Silcris26/Rover-Gale/Diagramas/Diagrama Caja Negra.png

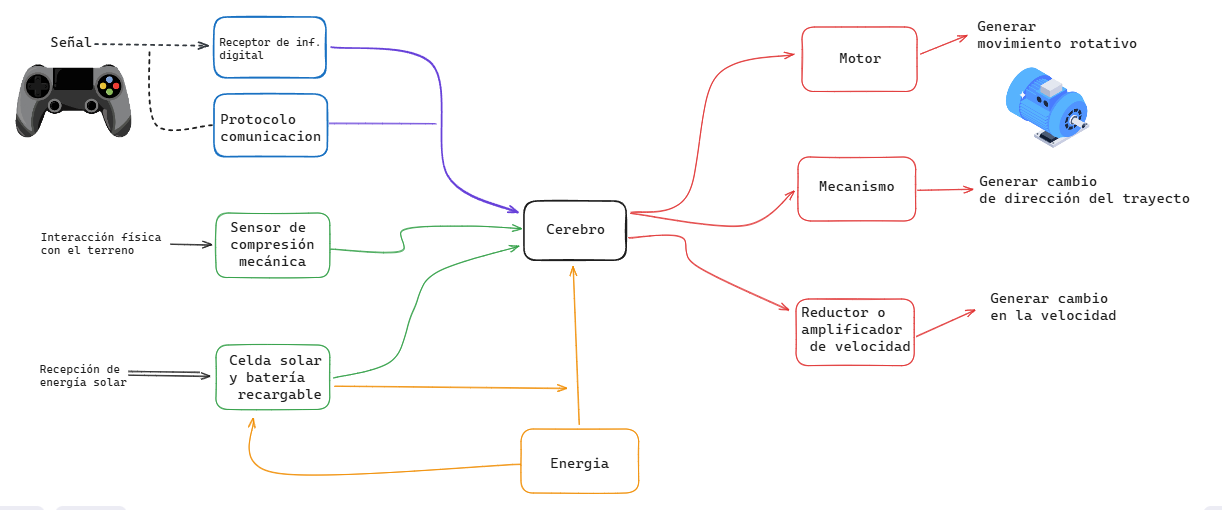
Diagramas/Diagrama Caja Negra.png
