Silcris26/Rover-Gale/Diagramas/Diagrama Codigo.png

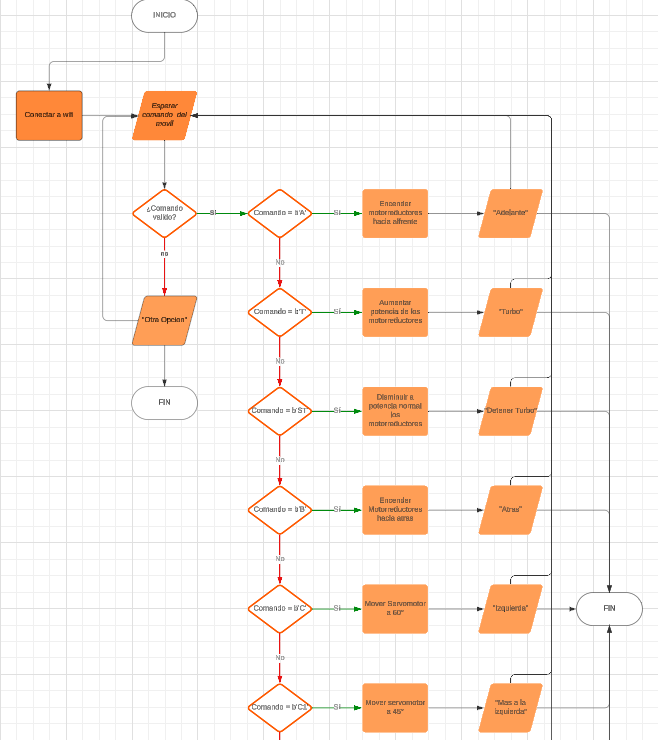
Diagramas/Diagrama Codigo.png
