Silcris26/Rover-Gale/Diagramas/Diagrama tecnologia.PNG

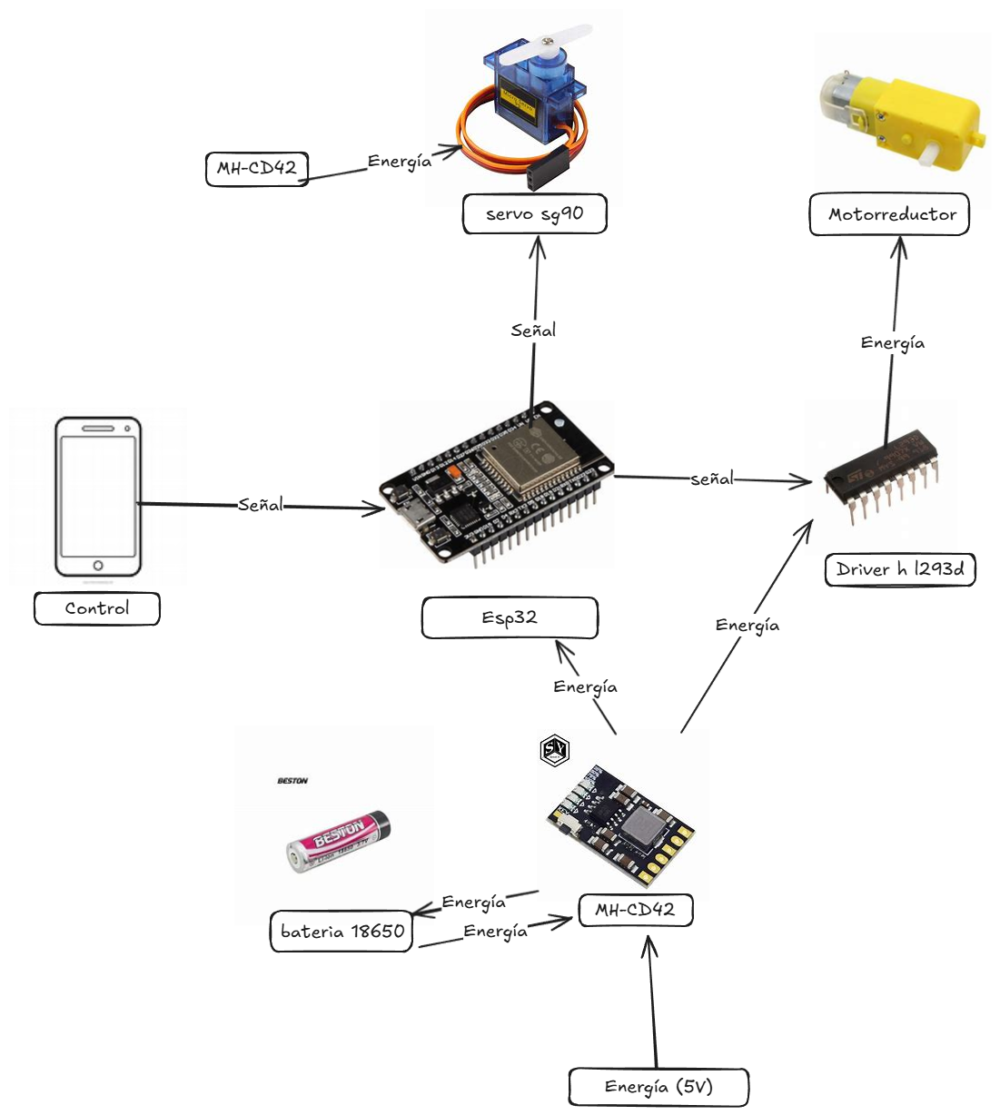
Diagramas/Diagrama tecnologia.PNG
