Silcris26/Rover-Gale/Diseño 3D/1.jpg

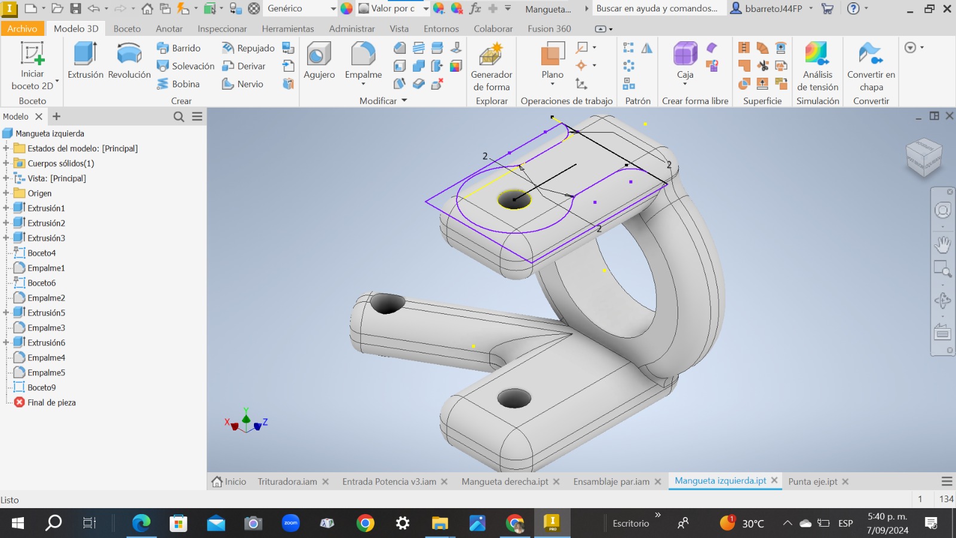
Diseño 3D/1.jpg
