Silcris26/Rover-Gale/Diseño 3D/2.jpg

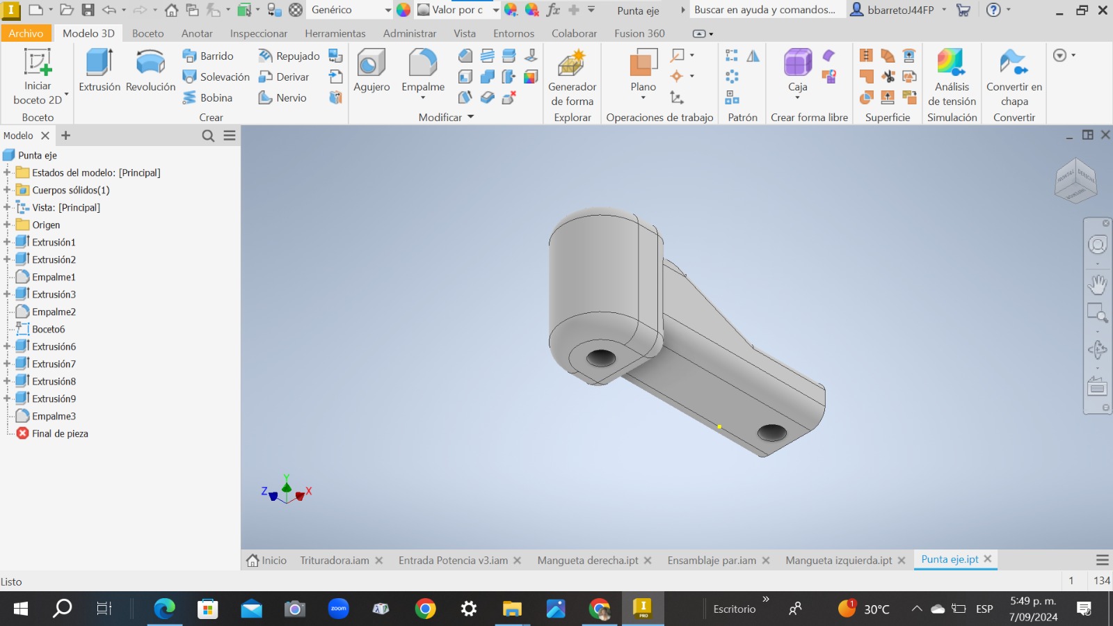
Diseño 3D/2.jpg
