Silcris26/Rover-Gale/Diseño 3D/4.jpg

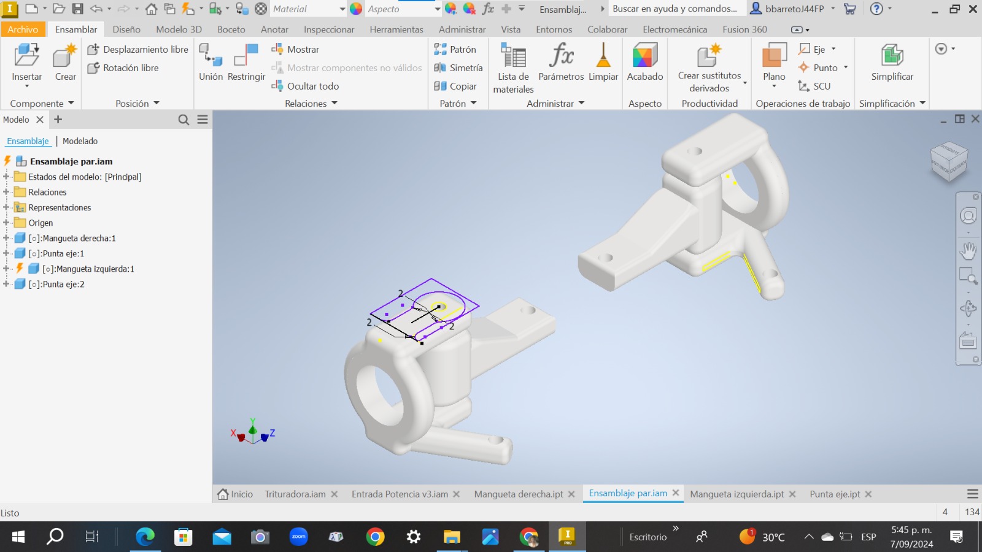
Diseño 3D/4.jpg
