Silcris26/Rover-Gale/Diseño 3D/5.jpg

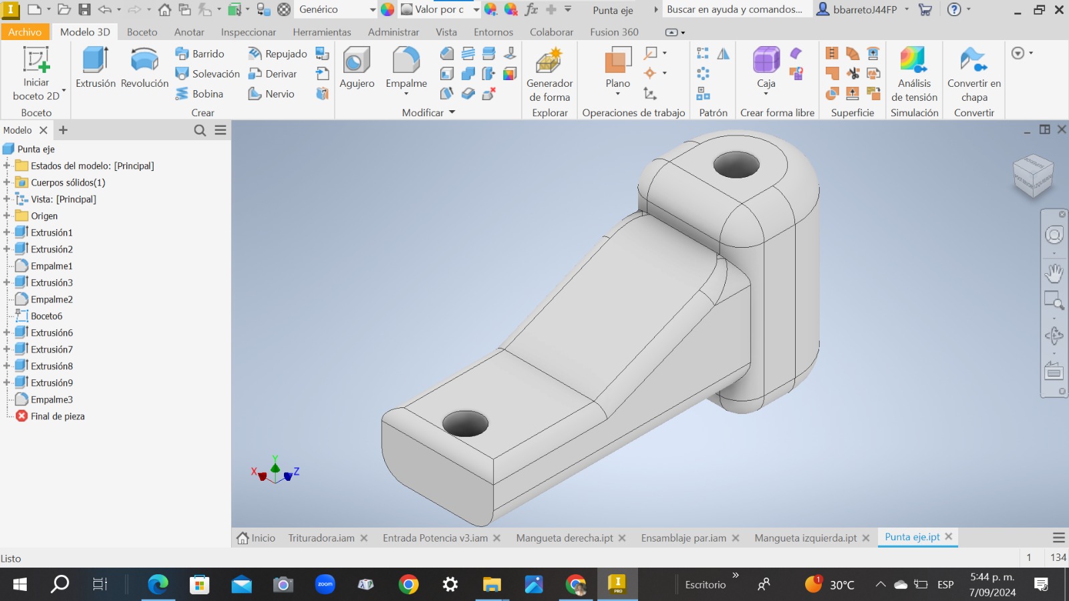
Diseño 3D/5.jpg
