Silcris26/Rover-Gale/Diseño 3D/7.jpg

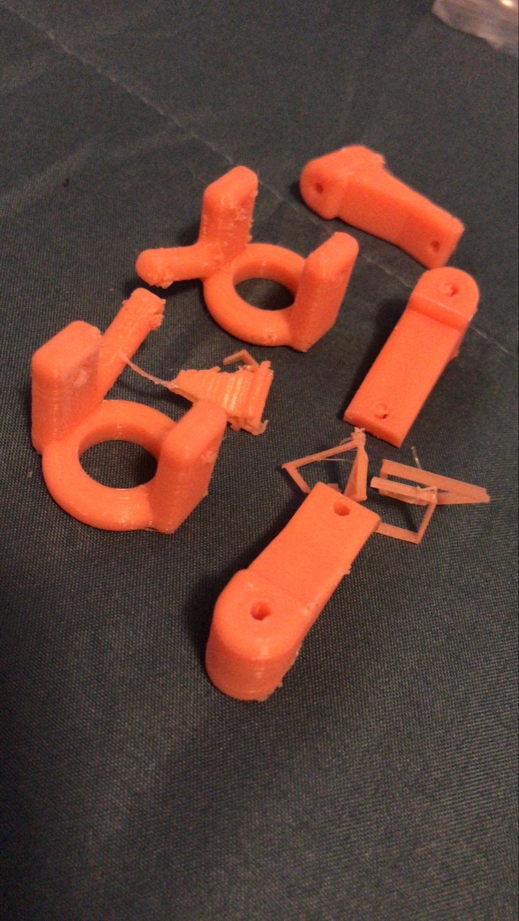
Diseño 3D/7.jpg
