Silcris26/Rover-Gale/Diseño 3D/8.jpg

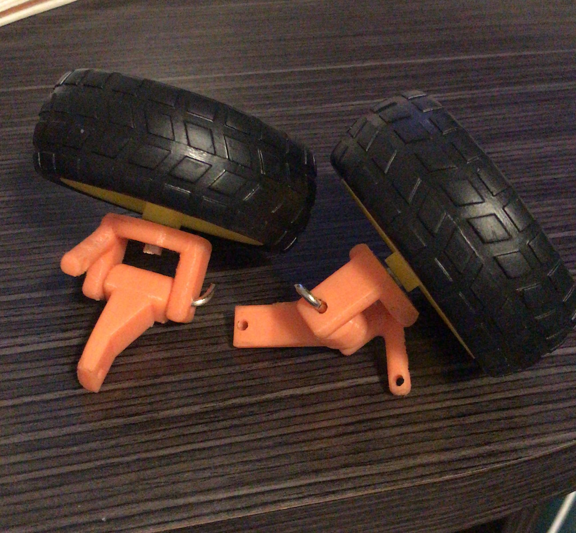
Diseño 3D/8.jpg
