Silcris26/Rover-Gale/Imagenes de evidencia/IMG1.jpeg

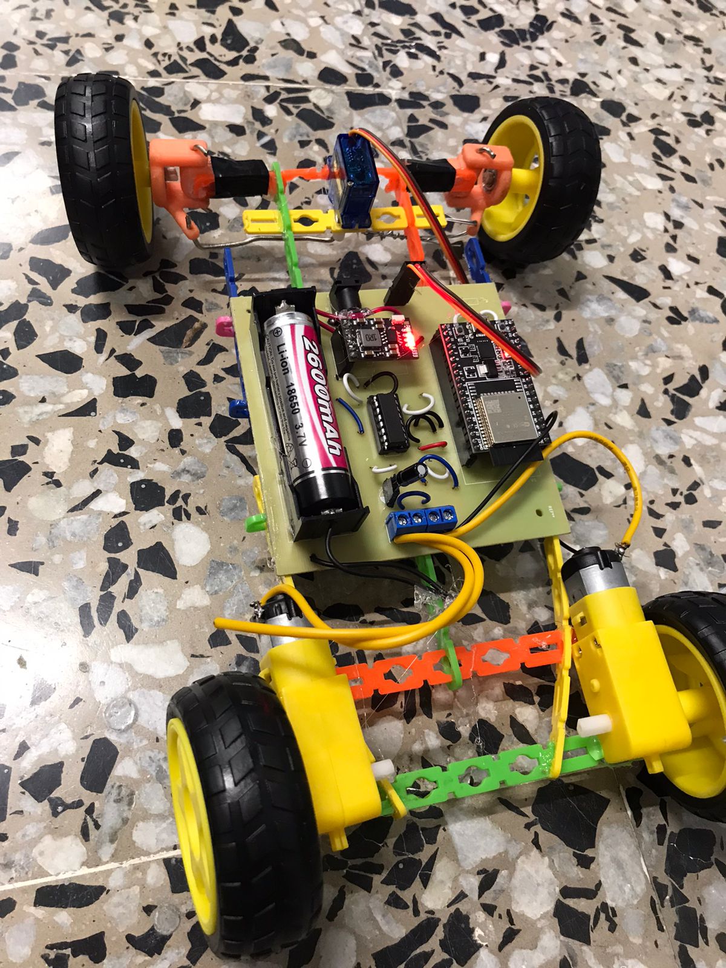
Imagenes de evidencia/IMG1.jpeg
