Silcris26/Rover-Gale/Imagenes de evidencia/IMG2.jpeg

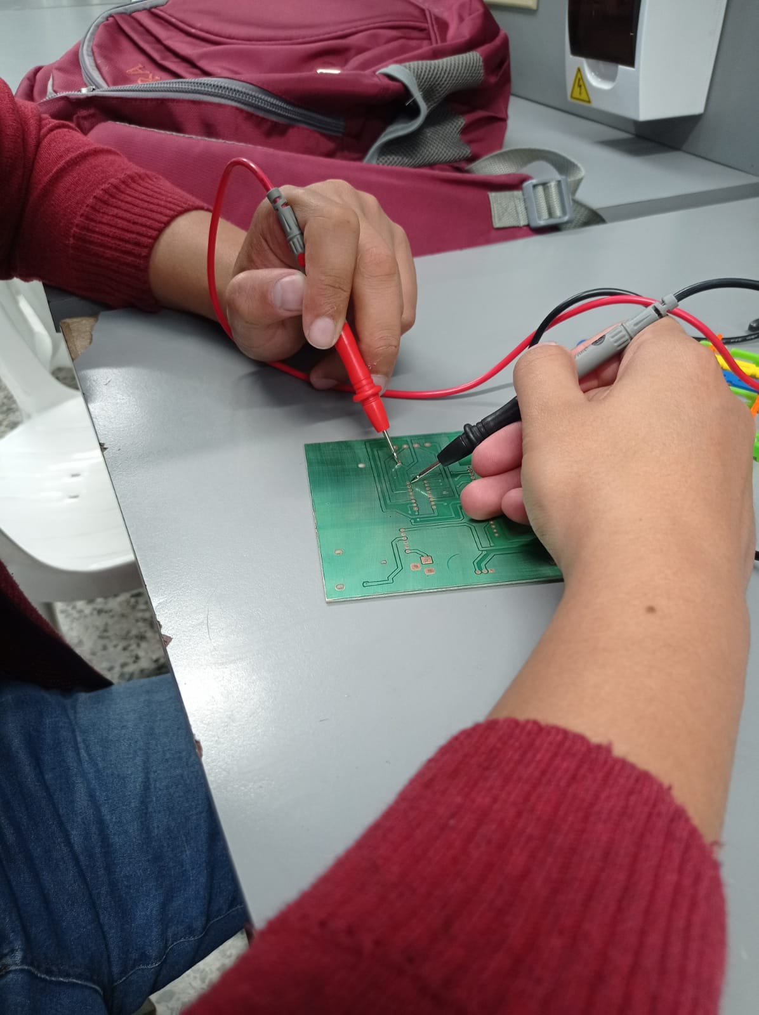
Imagenes de evidencia/IMG2.jpeg
