Silcris26/Rover-Gale/Imagenes de evidencia/IMG3.jpeg

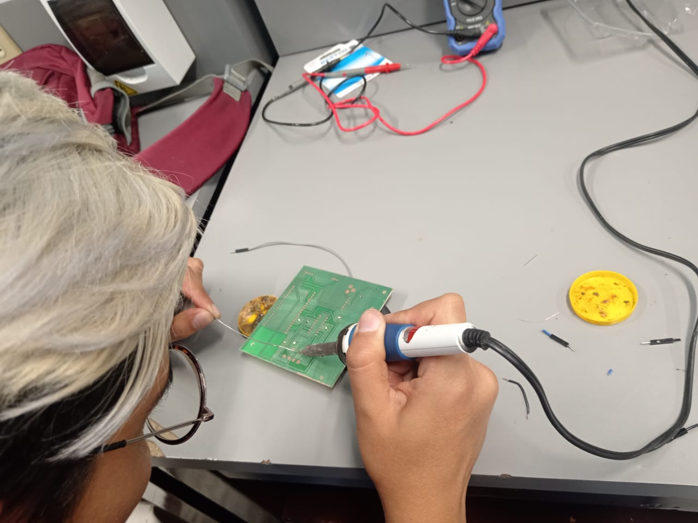
Imagenes de evidencia/IMG3.jpeg
