Silcris26/Rover-Gale/Imagenes de evidencia/IMG4.jpeg

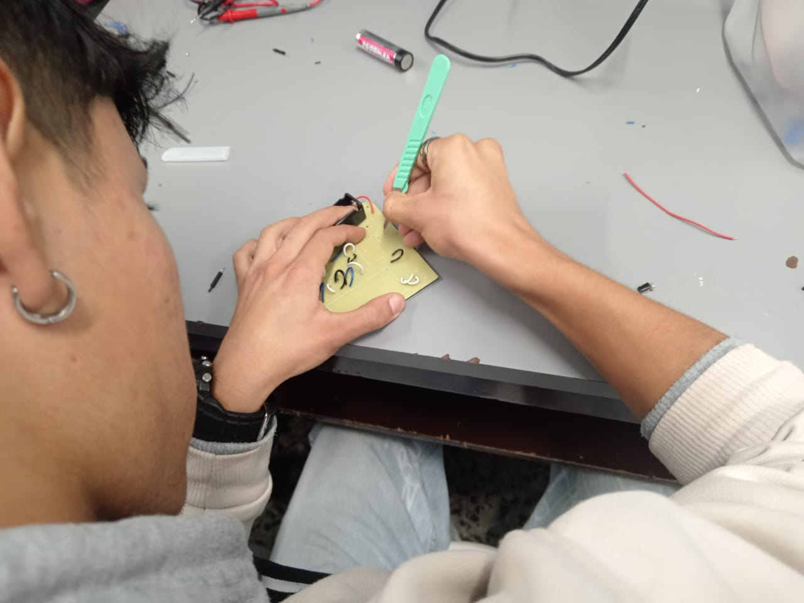
Imagenes de evidencia/IMG4.jpeg
