Silcris26/Rover-Gale/Imagenes de evidencia/IMG5.jpeg

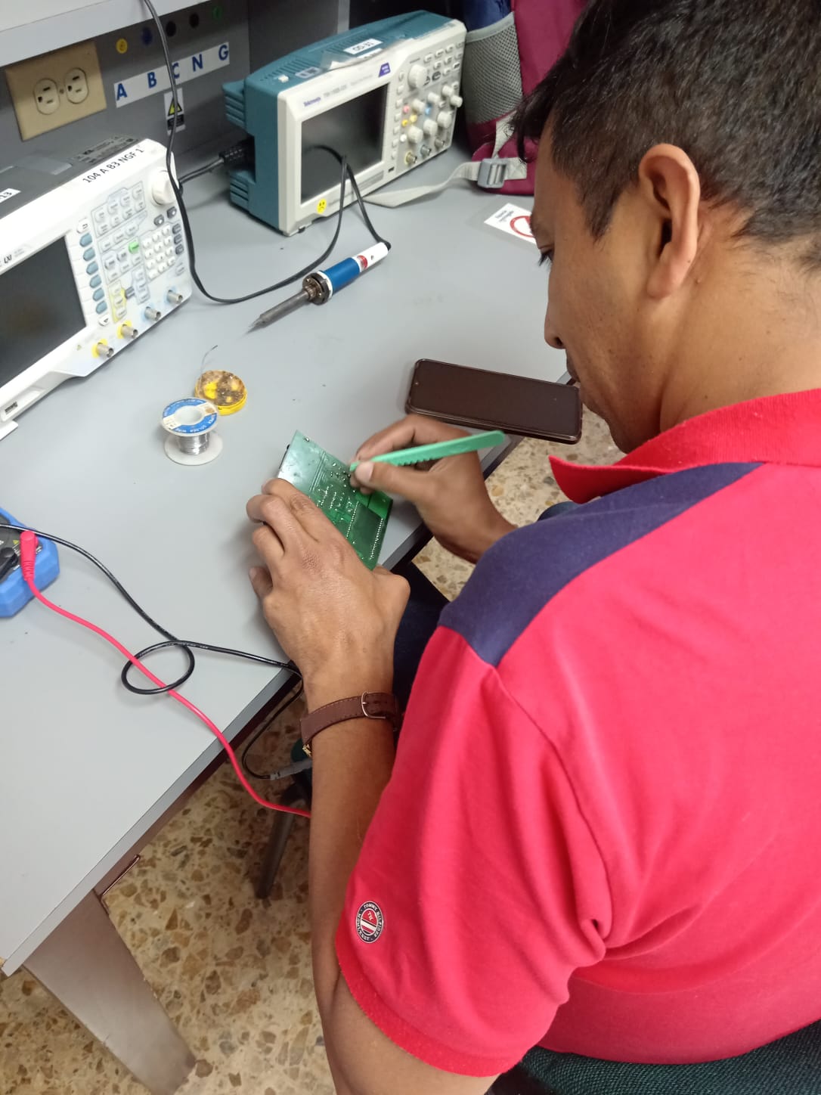
Imagenes de evidencia/IMG5.jpeg
