Silcris26/Rover-Gale/Imagenes de evidencia/IMG6.jpeg

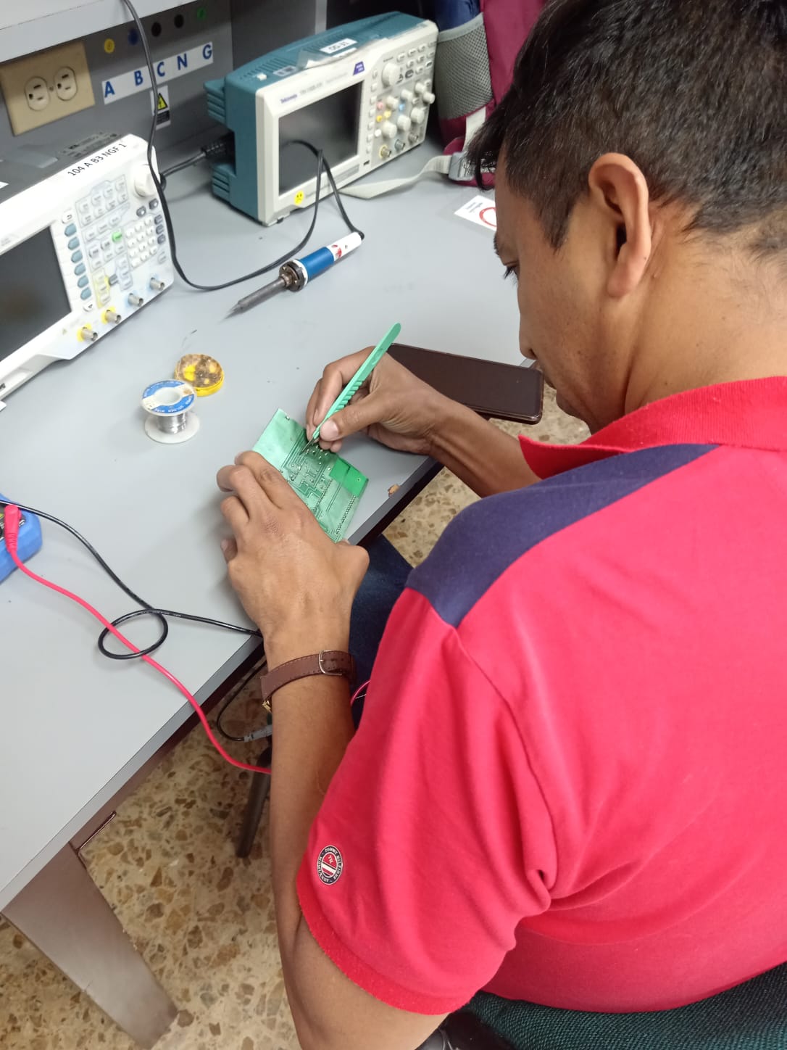
Imagenes de evidencia/IMG6.jpeg
