Silcris26/Rover-Gale/Imagenes de evidencia/IMG7.jpeg

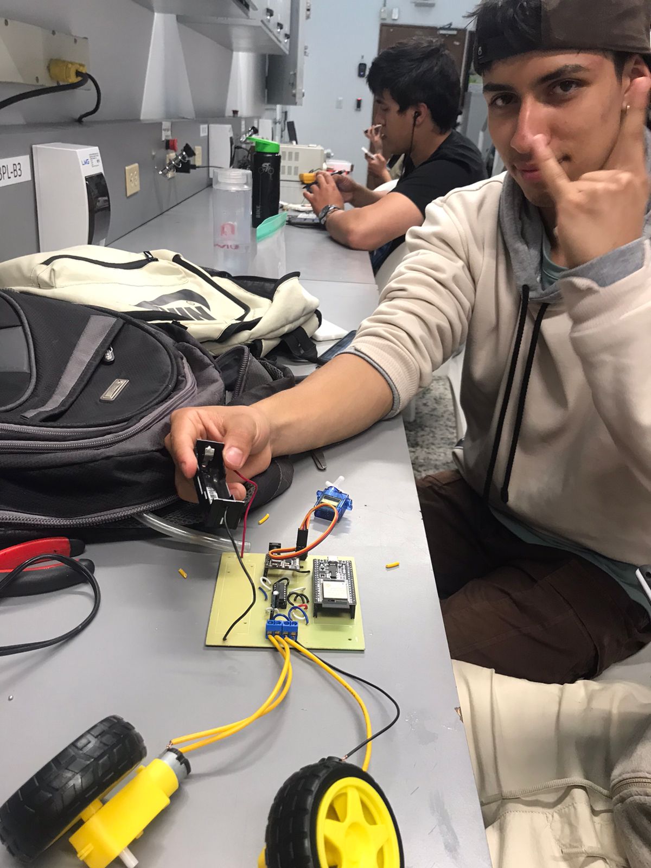
Imagenes de evidencia/IMG7.jpeg
