Silcris26/Rover-Gale/Imagenes de evidencia/IMG8.jpeg

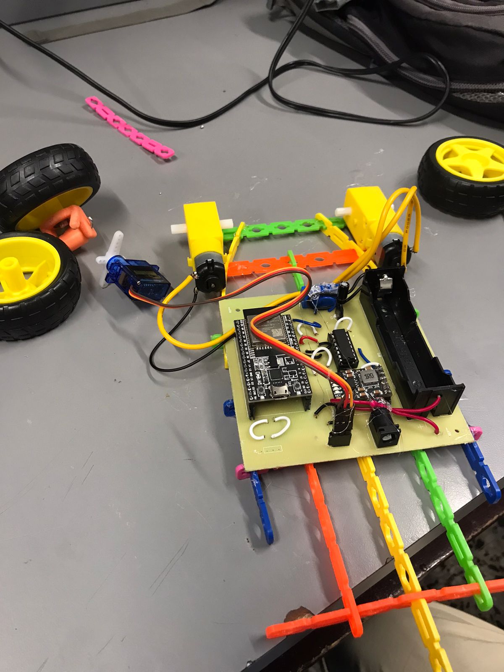
Imagenes de evidencia/IMG8.jpeg
