Silcris26/Rover-Gale/Imagenes de evidencia/IMG9.jpeg

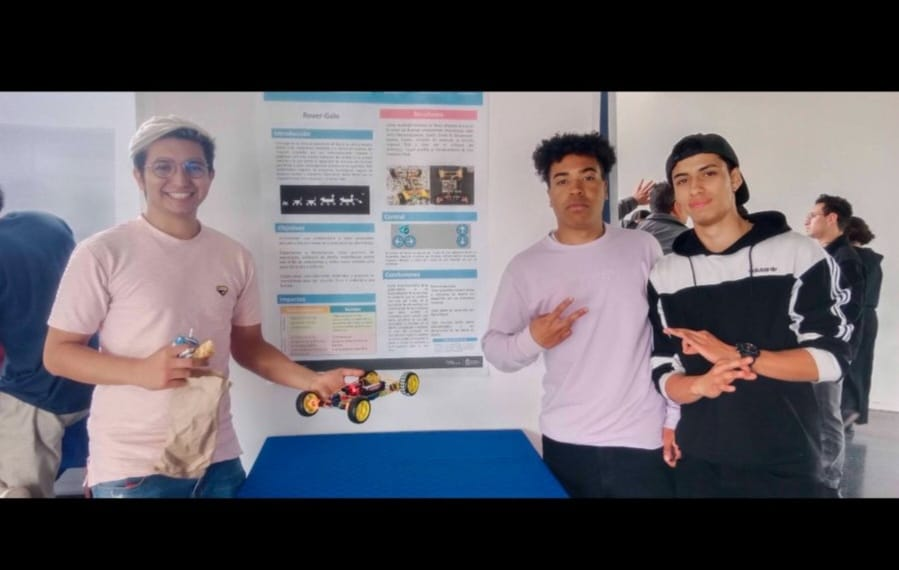
Imagenes de evidencia/IMG9.jpeg
