Silcris26/Rover-Gale/Imagenes de evidencia/IMG11.png

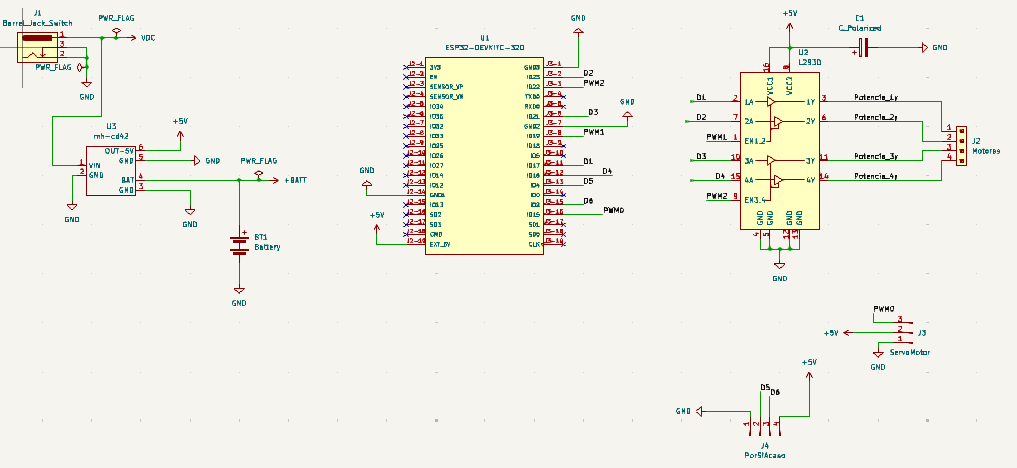
Imagenes de evidencia/IMG11.png
