Silcris26/Rover-Gale/Imagenes de evidencia/IMG12.png

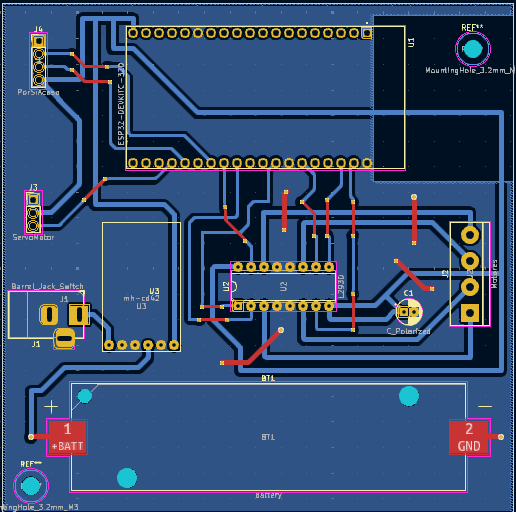
Imagenes de evidencia/IMG12.png
