Silcris26/Rover-Gale/Imagenes de evidencia/IMG13.png

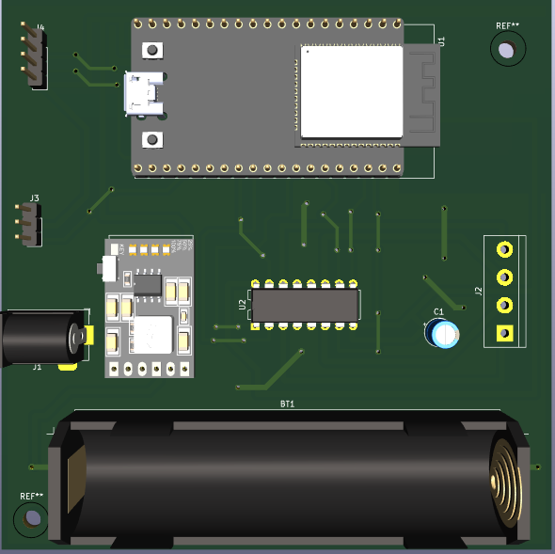
Imagenes de evidencia/IMG13.png
