Silcris26/Rover-Gale/Imagenes de evidencia/IMG14.png

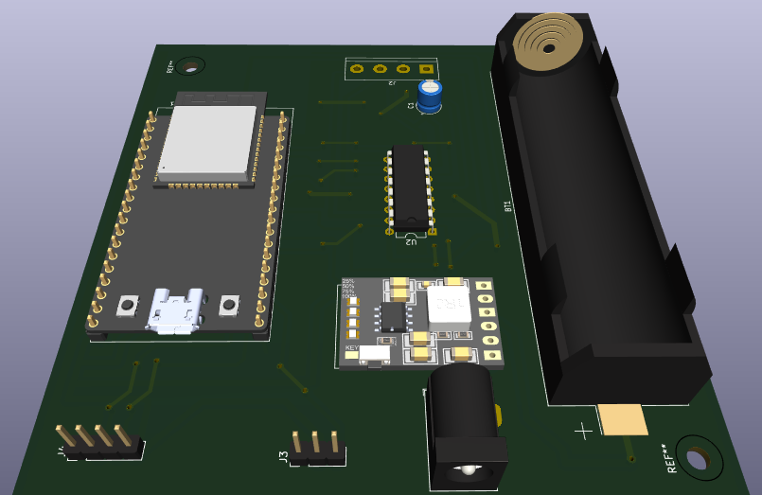
Imagenes de evidencia/IMG14.png
