Silcris26/Rover-Gale/Imagenes de evidencia/IMG16.png

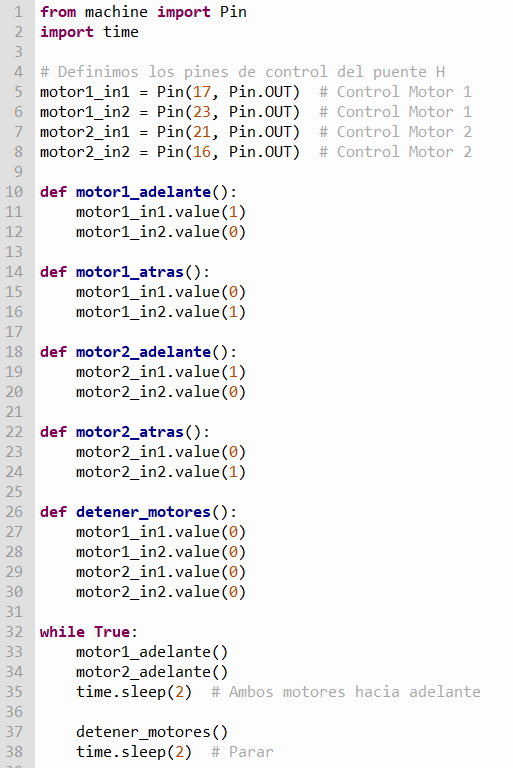
Imagenes de evidencia/IMG16.png
