Silcris26/Rover-Gale/Imagenes de evidencia/IMG17.png

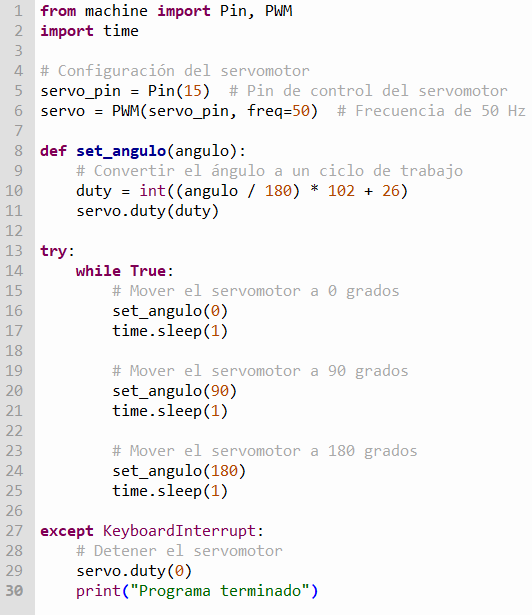
Imagenes de evidencia/IMG17.png
