Silcris26/Rover-Gale/Imagenes de evidencia/IMG18.png

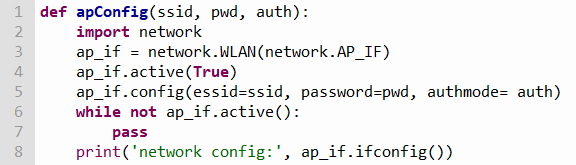
Imagenes de evidencia/IMG18.png
