Silcris26/Rover-Gale/Imagenes de evidencia/IMG19.png

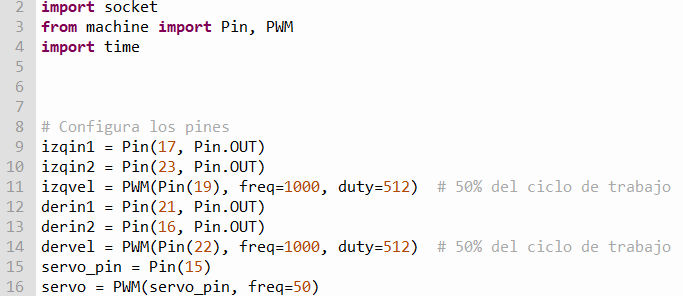
Imagenes de evidencia/IMG19.png
