Silcris26/Rover-Gale/Imagenes de evidencia/IMG20.png

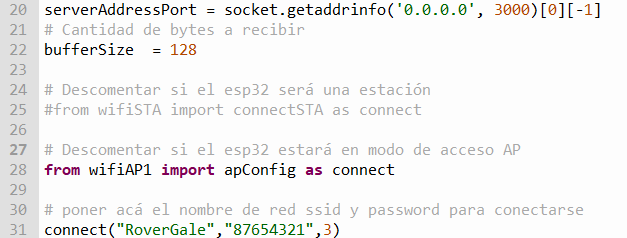
Imagenes de evidencia/IMG20.png
