Silcris26/Rover-Gale/Imagenes de evidencia/IMG22.png

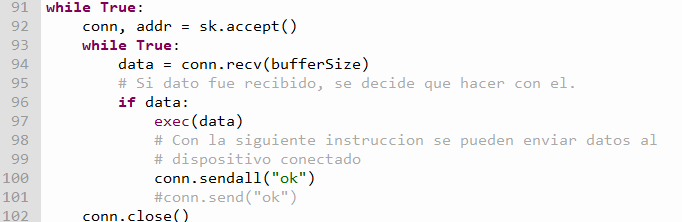
Imagenes de evidencia/IMG22.png
