Silcris26/Rover-Gale/Imagenes de evidencia/IMG23.png

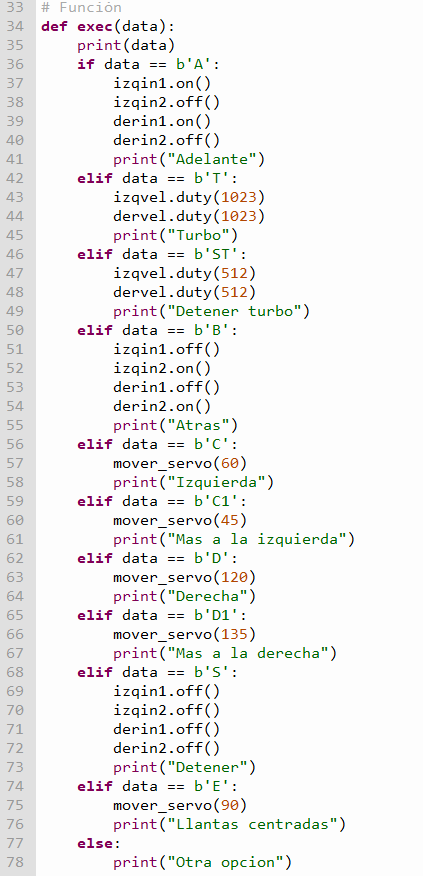
Imagenes de evidencia/IMG23.png
