Silcris26/Rover-Gale/Imagenes de evidencia/IMG25.jpg

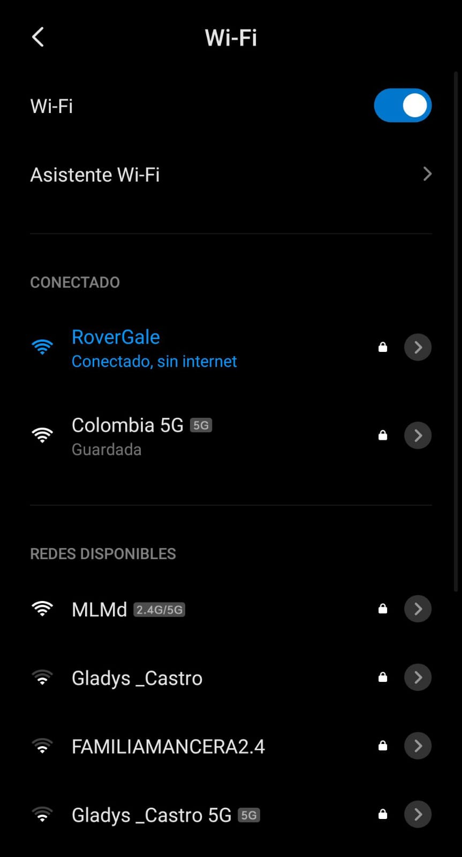
Imagenes de evidencia/IMG25.jpg
