Silcris26/Rover-Gale/Imagenes de evidencia/IMG26.png

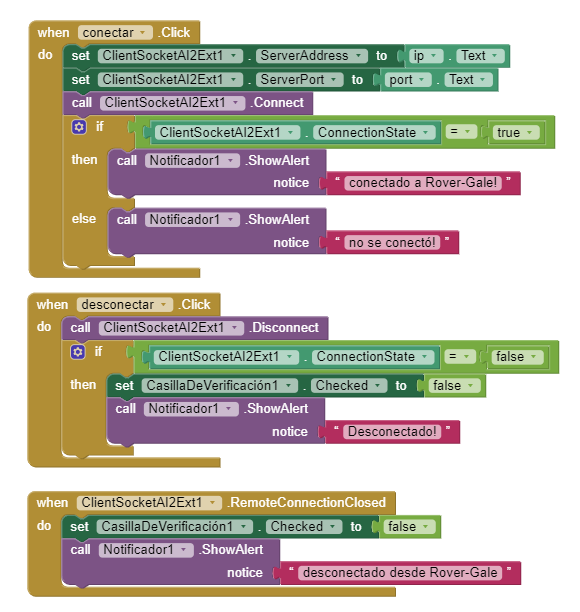
Imagenes de evidencia/IMG26.png
