Silcris26/Rover-Gale/Imagenes de evidencia/IMG27.png

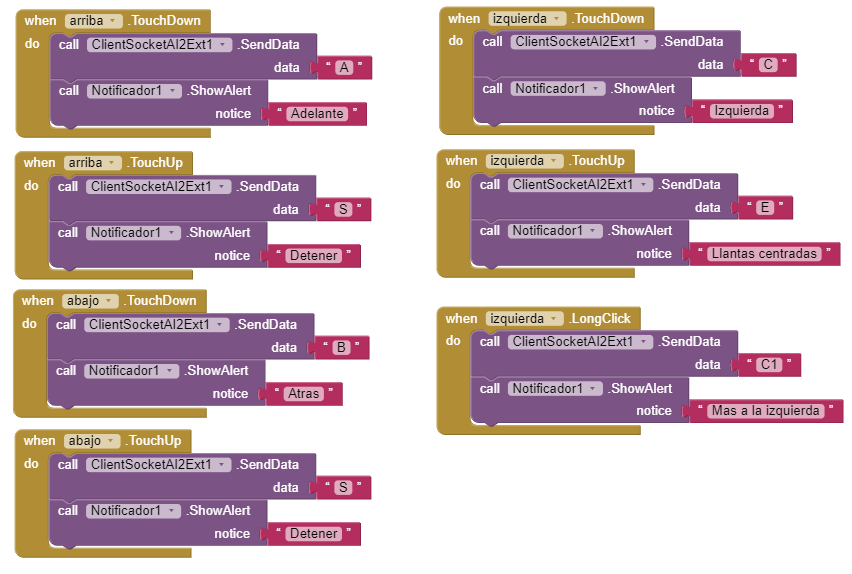
Imagenes de evidencia/IMG27.png
