Silcris26/Rover-Gale/Imagenes de evidencia/IMG28.png

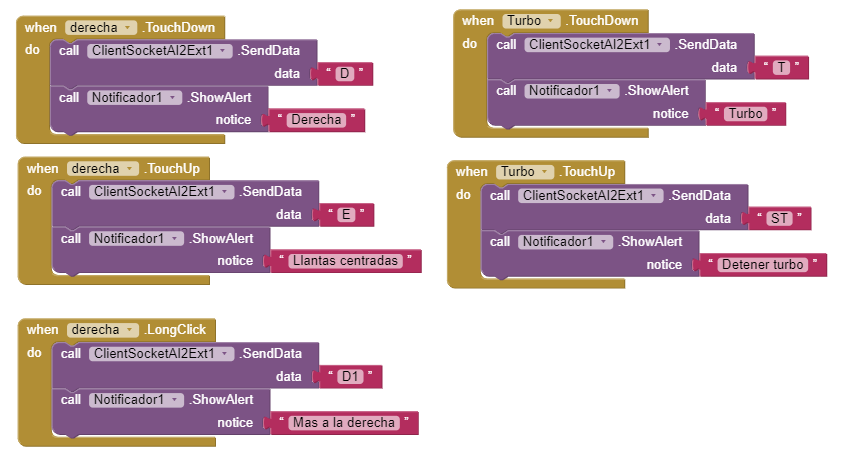
Imagenes de evidencia/IMG28.png
