Silcris26/Rover-Gale/Imagenes de evidencia/IMG29.jpeg

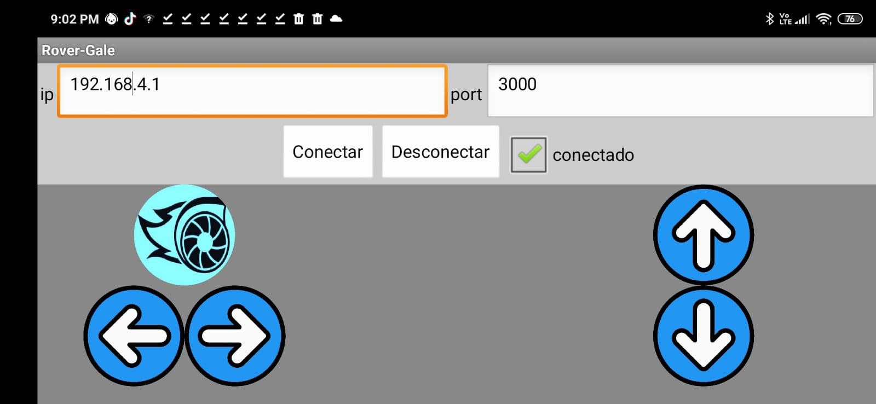
Imagenes de evidencia/IMG29.jpeg
